gratinDeTopinambour/Epaper_Clock_stm32/Stm32 Code/STM32F103CB/Drivers/EPAPER_lib/Inc/EPAPER_LUT.h

#ifndef EPAPER_LUT_H_
#define EPAPER_LUT_H_

#include <stdint.h>

extern const uint8_t EPAPER_lut_vcom[];
extern const uint8_t EPAPER_lut_ww[];
extern const uint8_t EPAPER_lut_bw[];
extern const uint8_t EPAPER_lut_wb[];
extern const uint8_t EPAPER_lut_bb[];

#endif /* EPAPER_LIB_INC_EPAPER_LUT_H_ */
