gratinDeTopinambour/Epaper_Clock_stm32/Stm32 Code/STM32F103CB/Drivers/EPAPER_lib/Inc/pixel_font.h

/*
 * pixel_font.h
 *
 *  Created on: Jan 17, 2026
 *      Author: valentin
 */

#ifndef EPAPER_LIB_INC_PIXEL_FONT_H_
#define EPAPER_LIB_INC_PIXEL_FONT_H_

#include <stdint.h>


extern const uint8_t bpixel[];
extern const uint8_t icone[];
extern const uint8_t moon[];


#endif /* EPAPER_LIB_INC_PIXEL_FONT_H_ */
