gratinDeTopinambour/Epaper_Clock_stm32/Stm32 Code/STM32F103CB/Drivers/EPAPER_lib/Src/EPAPER_LUT.c

#include "EPAPER_LUT.h"
//

/**
 * full screen update LUT
**/
const uint8_t EPAPER_lut_vcom[] = {
	0x01, 0x14, 0x0A, 0x00, 0x00, 0x01, 0x01,
	0x01, 0x00, 0x00, 0x00, 0x00, 0x01, 0x01,
	0x01, 0x00, 0x00, 0x00, 0x00, 0x01, 0x01,
	0x01, 0x00, 0x00, 0x00, 0x00, 0x01, 0x01,
	0x01, 0x00, 0x00, 0x00, 0x00, 0x01, 0x01,
	0x01, 0x00, 0x00, 0x00, 0x00, 0x01, 0x01,
};

const uint8_t EPAPER_lut_ww[] = {
	0x01, 0x14, 0x0A, 0x00, 0x00, 0x01, 0x01,
	0x01, 0x00, 0x00, 0x00, 0x00, 0x01, 0x01,
	0x01, 0x00, 0x00, 0x00, 0x00, 0x01, 0x01,
	0x01, 0x00, 0x00, 0x00, 0x00, 0x01, 0x01,
	0x01, 0x00, 0x00, 0x00, 0x00, 0x01, 0x01,
	0x01, 0x00, 0x00, 0x00, 0x00, 0x01, 0x01,
};

const uint8_t EPAPER_lut_bw[] = {
	0x01, 0x94, 0x0A, 0x00, 0x00, 0x01, 0x01,
	0x01, 0x00, 0x00, 0x00, 0x00, 0x01, 0x01,
	0x01, 0x00, 0x00, 0x00, 0x00, 0x01, 0x01,
	0x01, 0x00, 0x00, 0x00, 0x00, 0x01, 0x01,
	0x01, 0x00, 0x00, 0x00, 0x00, 0x01, 0x01,
	0x01, 0x00, 0x00, 0x00, 0x00, 0x01, 0x01,
};

const uint8_t EPAPER_lut_wb[] = {
	0x01, 0x54, 0x4A, 0x00, 0x00, 0x01, 0x01,
	0x01, 0x00, 0x00, 0x00, 0x00, 0x01, 0x01,
	0x01, 0x00, 0x00, 0x00, 0x00, 0x01, 0x01,
	0x01, 0x00, 0x00, 0x00, 0x00, 0x01, 0x01,
	0x01, 0x00, 0x00, 0x00, 0x00, 0x01, 0x01,
	0x01, 0x00, 0x00, 0x00, 0x00, 0x01, 0x01,
};

const uint8_t EPAPER_lut_bb[] = {
	0x01, 0x54, 0x4A, 0x00, 0x00, 0x01, 0x01,
	0x01, 0x00, 0x00, 0x00, 0x00, 0x01, 0x01,
	0x01, 0x00, 0x00, 0x00, 0x00, 0x01, 0x01,
	0x01, 0x00, 0x00, 0x00, 0x00, 0x01, 0x01,
	0x01, 0x00, 0x00, 0x00, 0x00, 0x01, 0x01,
	0x01, 0x00, 0x00, 0x00, 0x00, 0x01, 0x01,
};
